fcl2002/Open-Ruche-Monitoring/hardware/3D_top.jpg

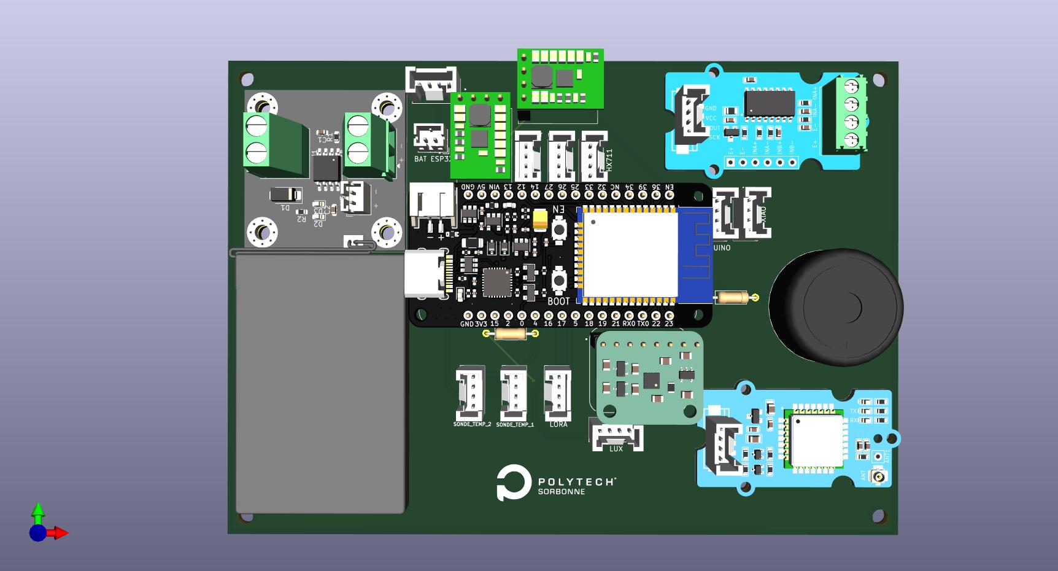
hardware/3D_top.jpg
